NuwanJ/peraSAP-I/PCBs/1. Clock/pdf/pcb_etch_copper_bottom.pdf

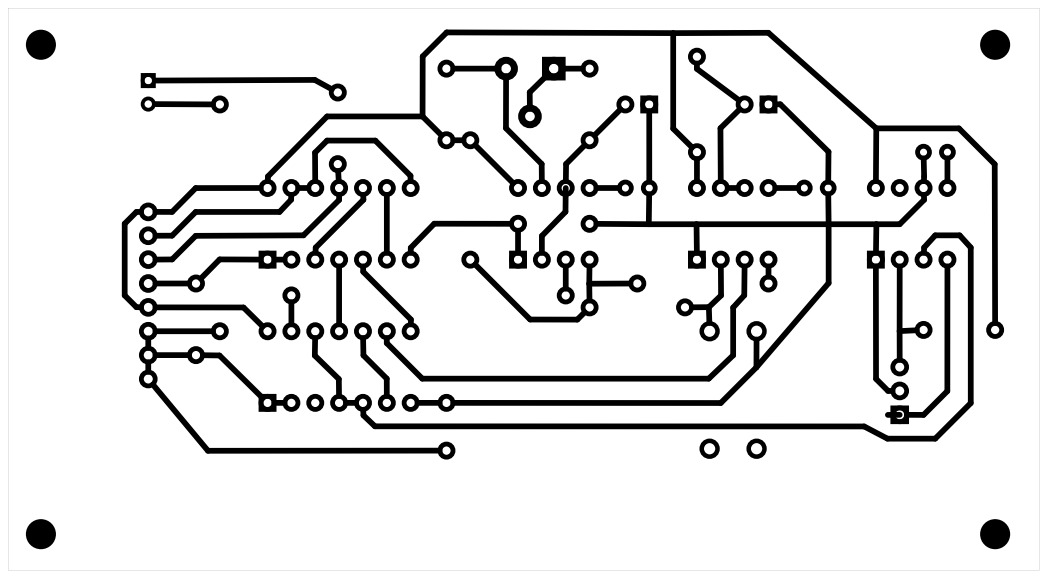
[picture p26: page 1]
