NuwanJ/peraSAP-I/PCBs/1. Clock/pdf/pcb_etch_copper_bottom_mirror.pdf

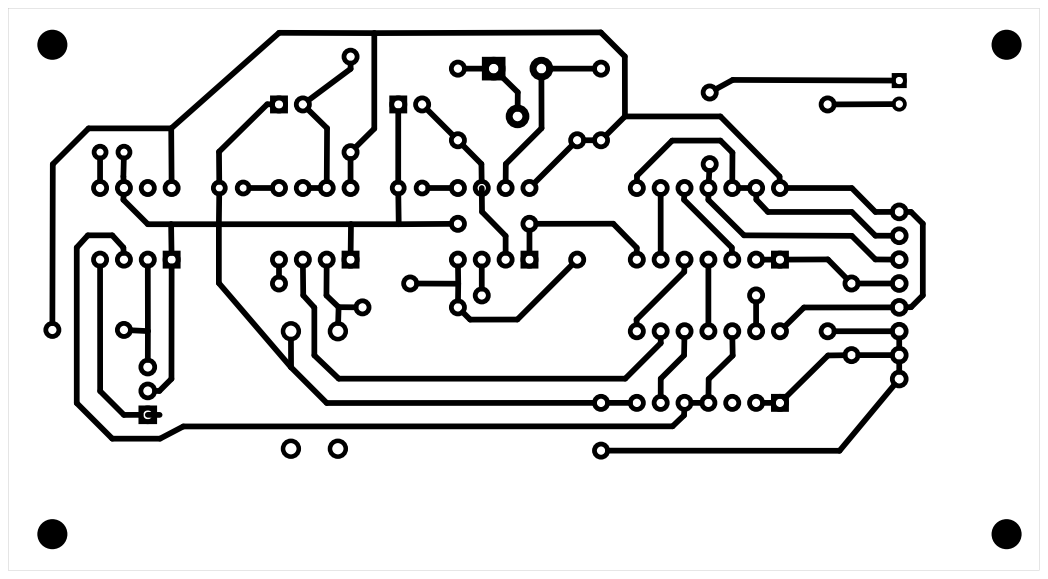
[picture p27: page 1]
