NuwanJ/peraSAP-I/PCBs/1. Clock/pdf/pcb_etch_copper_top.pdf

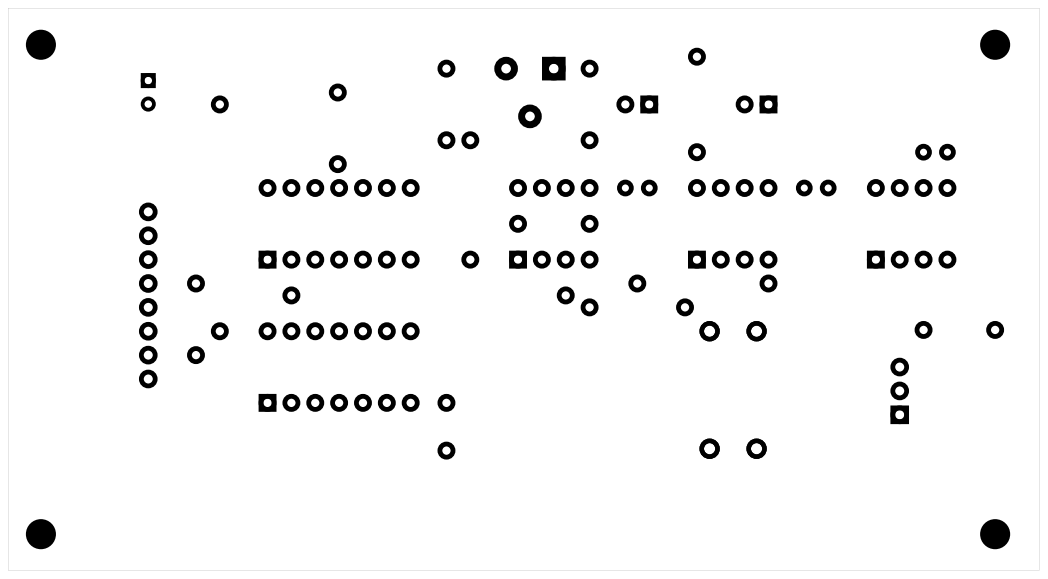
[picture p28: page 1]
