NuwanJ/peraSAP-I/PCBs/1. Clock/pdf/pcb_etch_copper_top_mirror.pdf

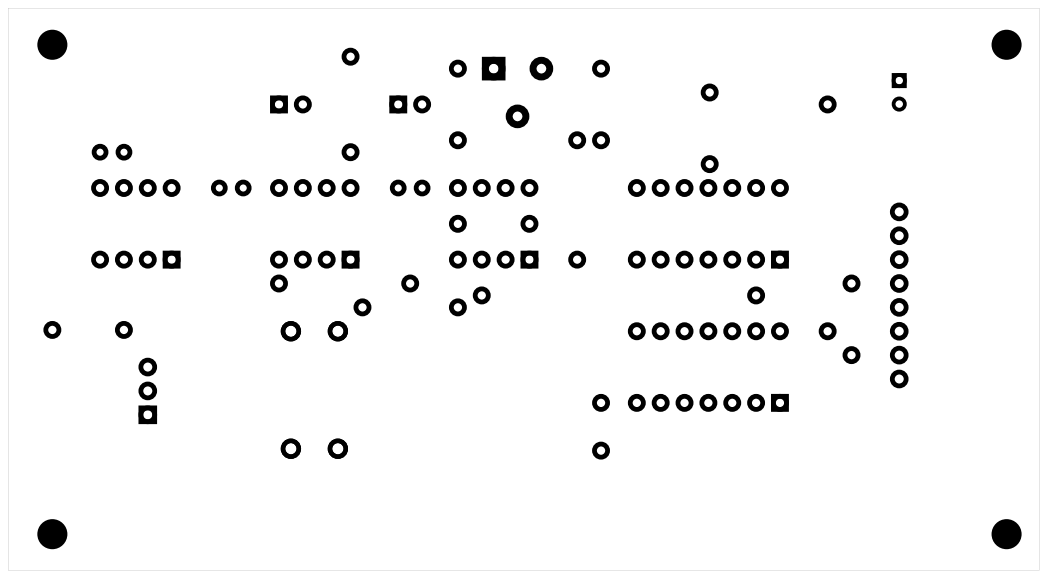
[picture p29: page 1]
