NuwanJ/peraSAP-I/PCBs/1. Clock/pdf/pcb_etch_mask_bottom.pdf

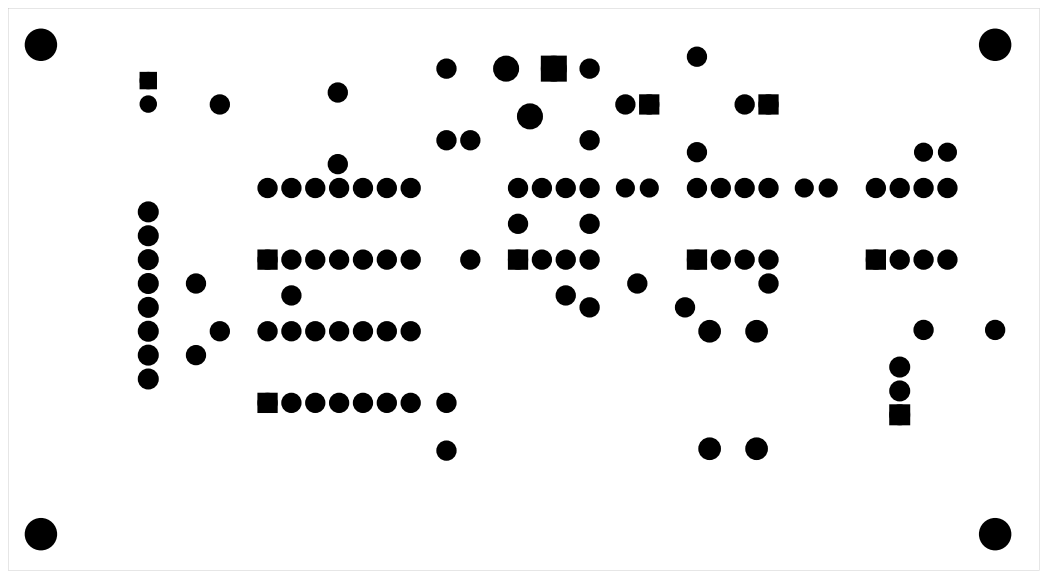
[picture p30: page 1]
