NuwanJ/peraSAP-I/PCBs/1. Clock/pdf/pcb_etch_mask_bottom_mirror.pdf

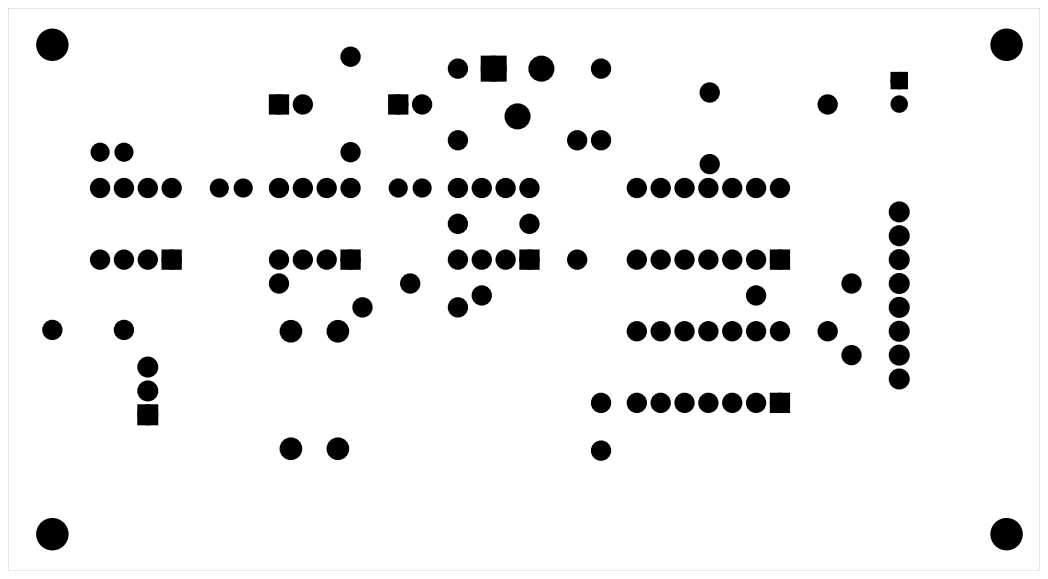
[picture p31: page 1]
