NuwanJ/peraSAP-I/PCBs/1. Clock/pdf/pcb_etch_mask_top.pdf

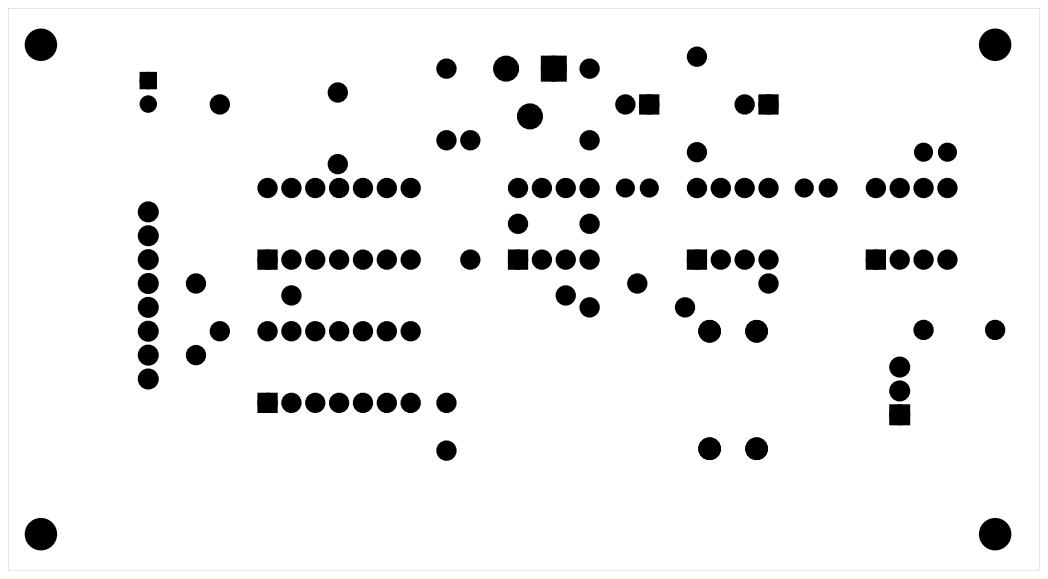
[picture p32: page 1]
