NuwanJ/peraSAP-I/PCBs/1. Clock/pdf/pcb_etch_mask_top_mirror.pdf

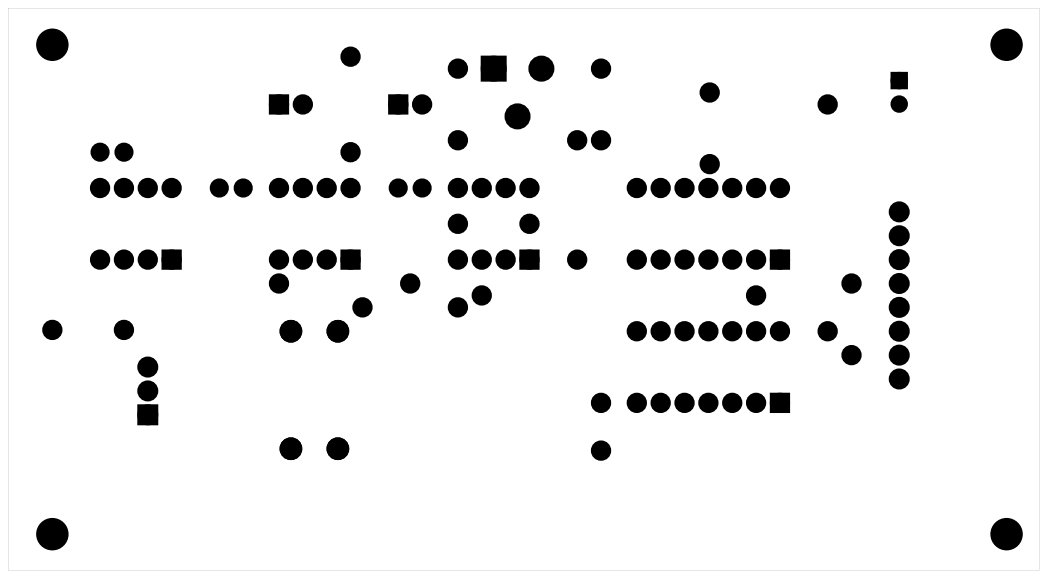
[picture p33: page 1]
