NuwanJ/peraSAP-I/PCBs/1. Clock/pdf/pcb_etch_silk_bottom.pdf

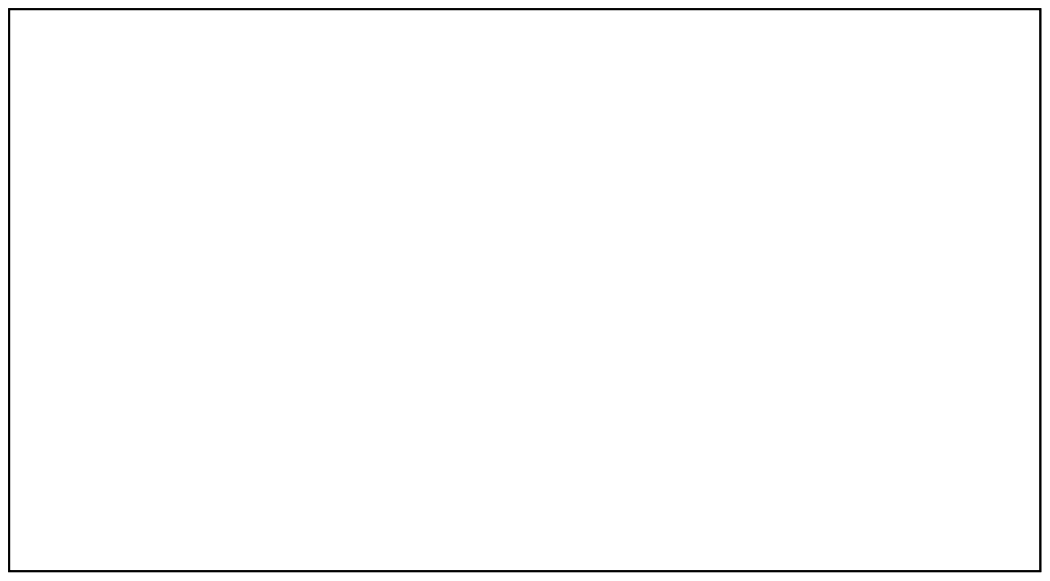
[picture p34: page 1]
