NuwanJ/peraSAP-I/PCBs/1. Clock/pdf/pcb_etch_silk_bottom_mirror.pdf

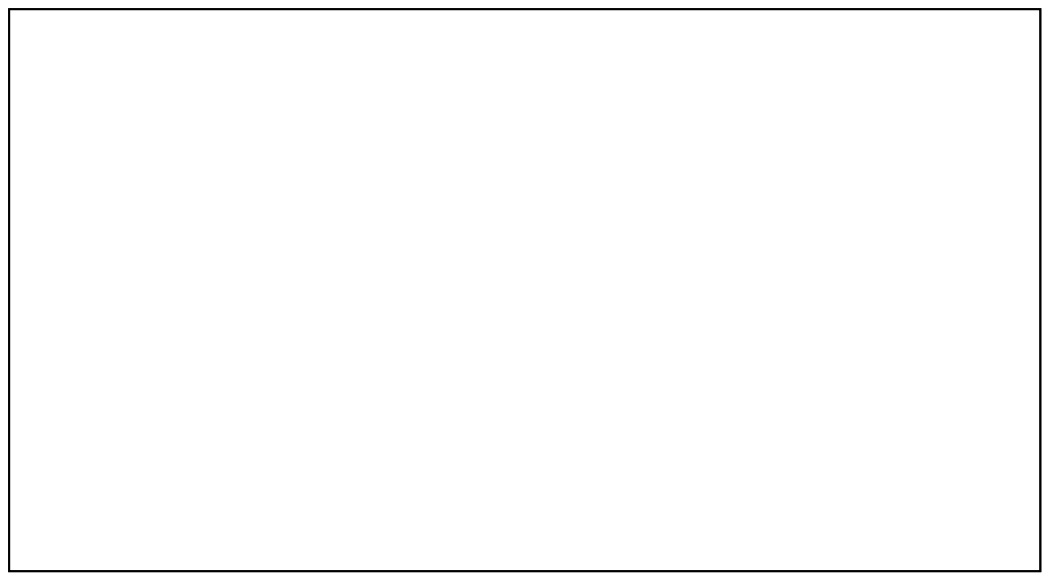
[picture p35: page 1]
