NuwanJ/peraSAP-I/PCBs/1. Clock/pdf/pcb_etch_silk_top.pdf

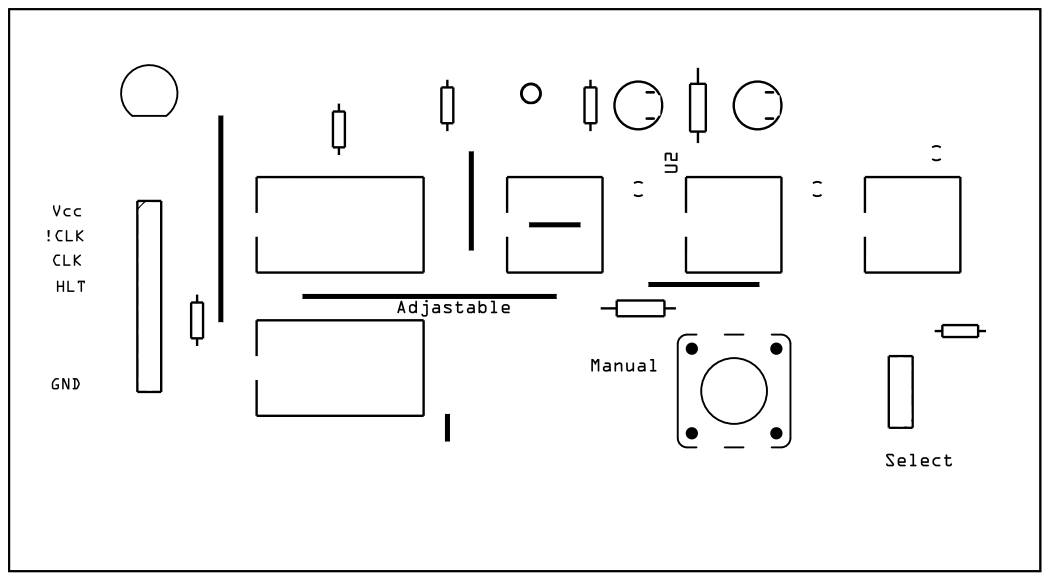
[picture p36: page 1]
