NuwanJ/peraSAP-I/PCBs/1. Clock/pdf/pcb_etch_silk_top_mirror.pdf

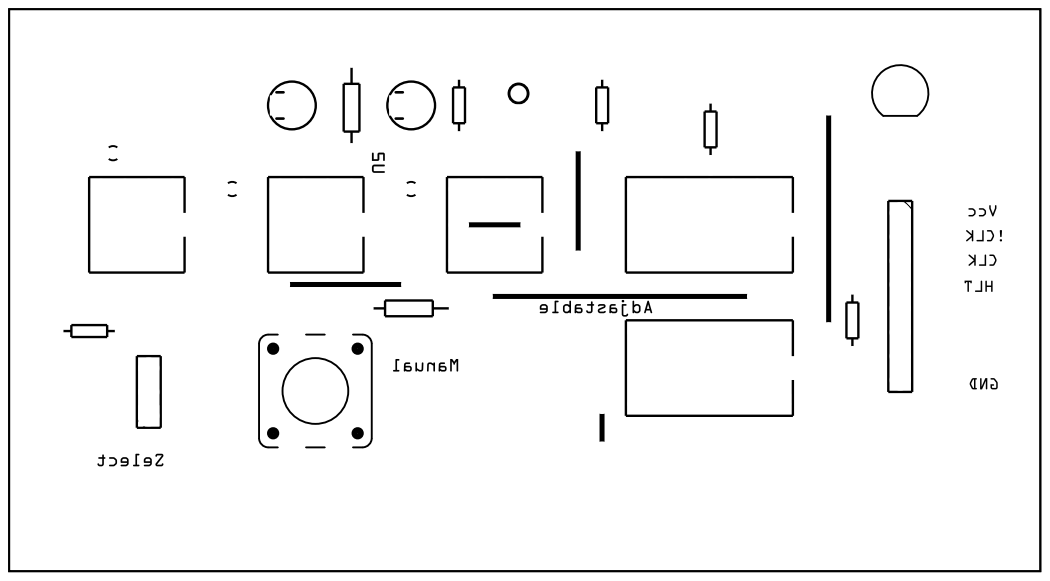
[picture p37: page 1]
