NuwanJ/peraSAP-I/PCBs/2. Registers/pdf/pcb_etch_copper_bottom.pdf

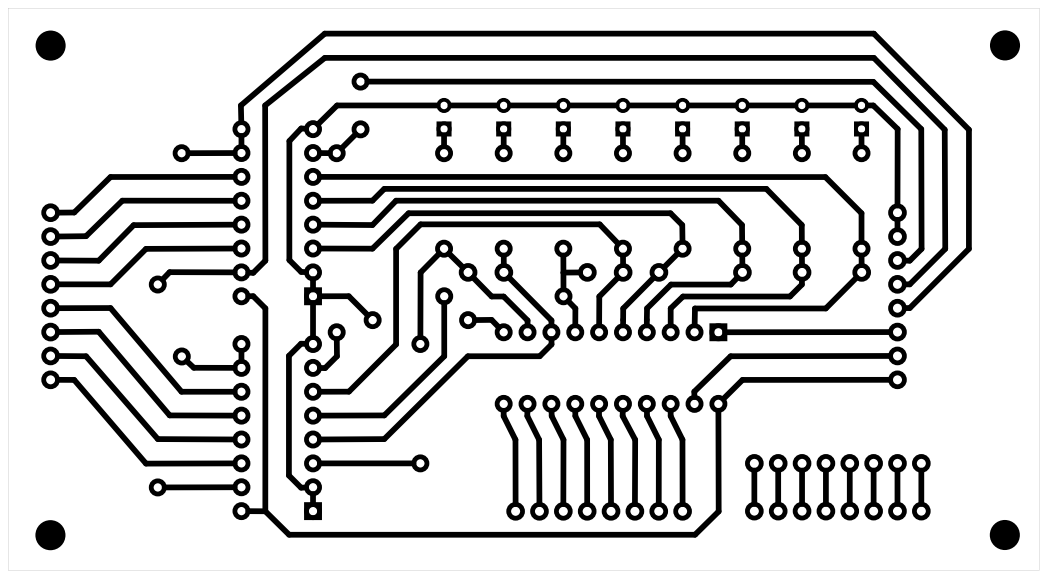
[picture p38: page 1]
