NuwanJ/peraSAP-I/PCBs/2. Registers/pdf/pcb_etch_copper_bottom_mirror.pdf

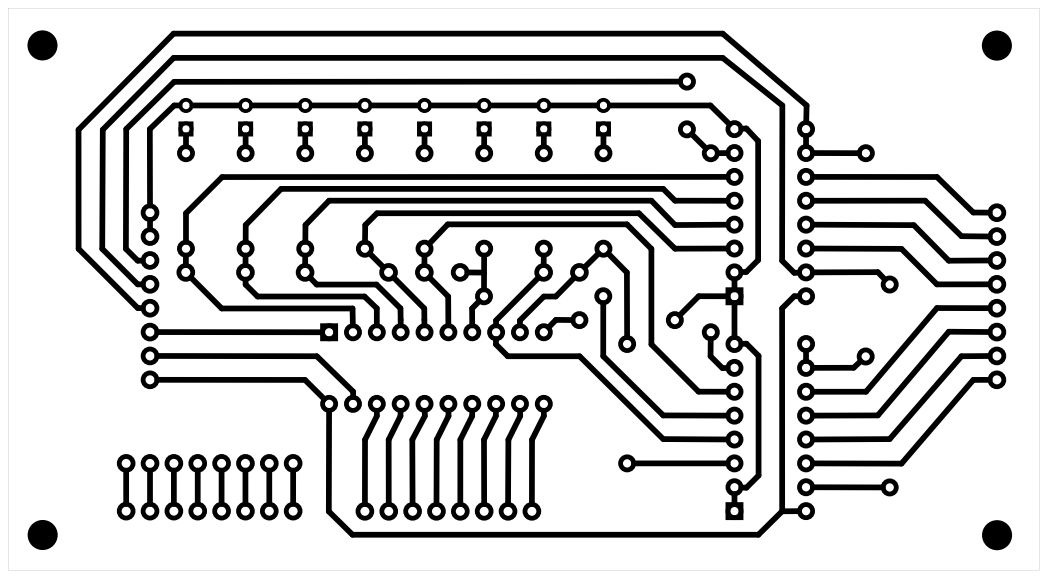
[picture p39: page 1]
