NuwanJ/peraSAP-I/PCBs/2. Registers/pdf/pcb_etch_mask_bottom.pdf

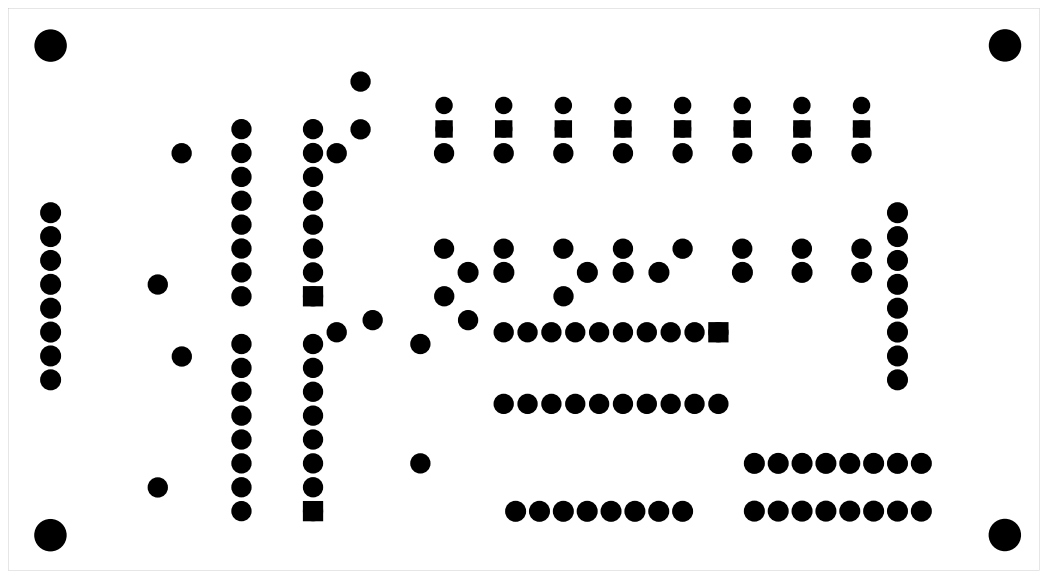
[picture p40: page 1]
