NuwanJ/peraSAP-I/PCBs/2. Registers/pdf/pcb_etch_mask_bottom_mirror.pdf

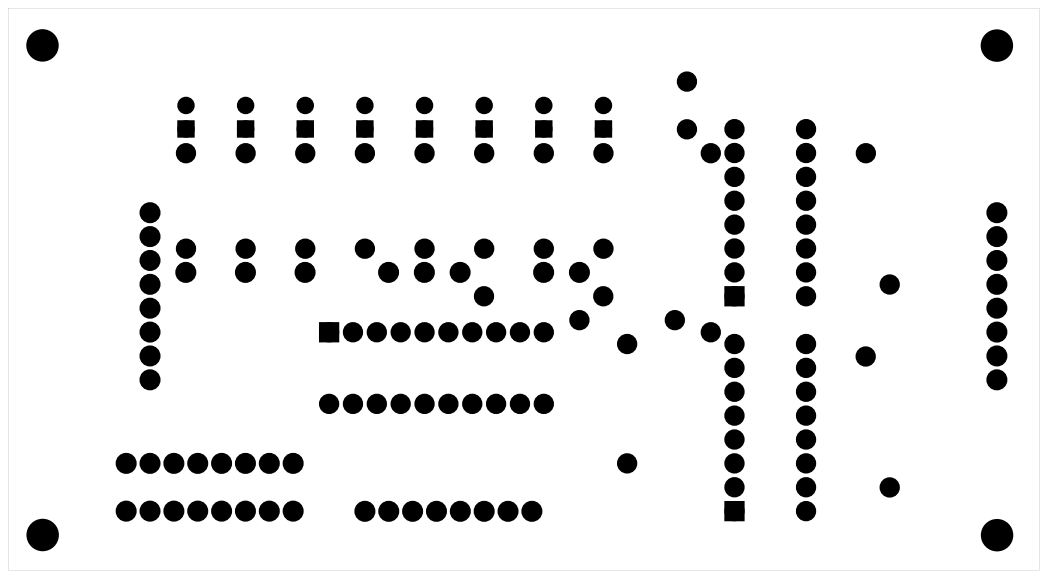
[picture p41: page 1]
