NuwanJ/peraSAP-I/PCBs/3. Program Counter/pdf/pcb3_etch_copper_bottom.pdf

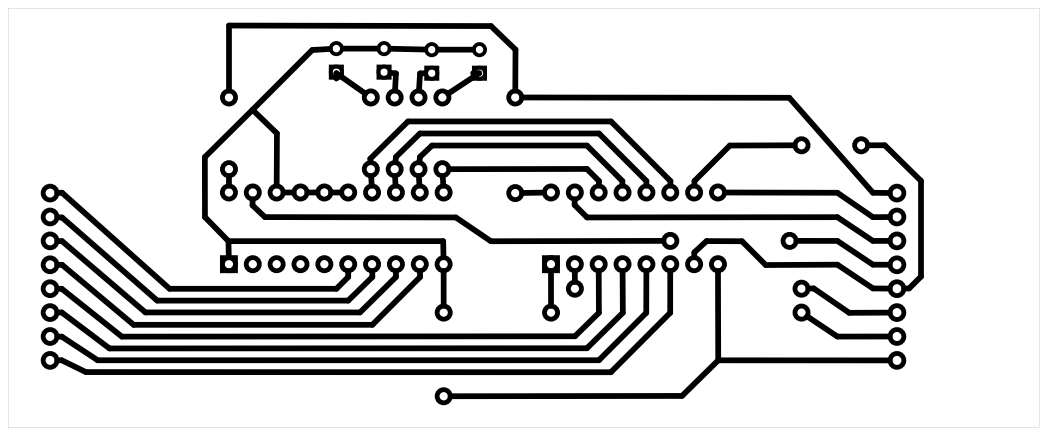
[picture p42: page 1]
