NuwanJ/peraSAP-I/PCBs/3. Program Counter/pdf/pcb3_etch_copper_bottom_mirror.pdf

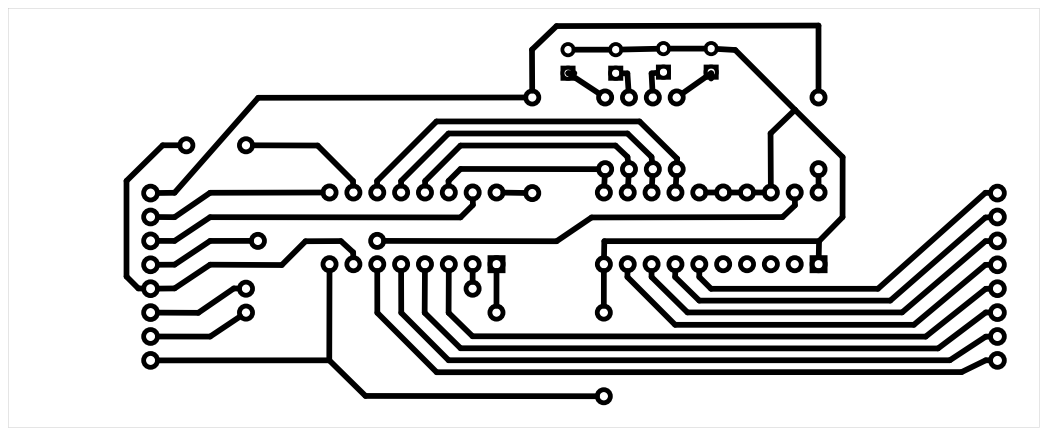
[picture p43: page 1]
