NuwanJ/peraSAP-I/PCBs/3. Program Counter/pdf/pcb3_etch_mask_bottom.pdf

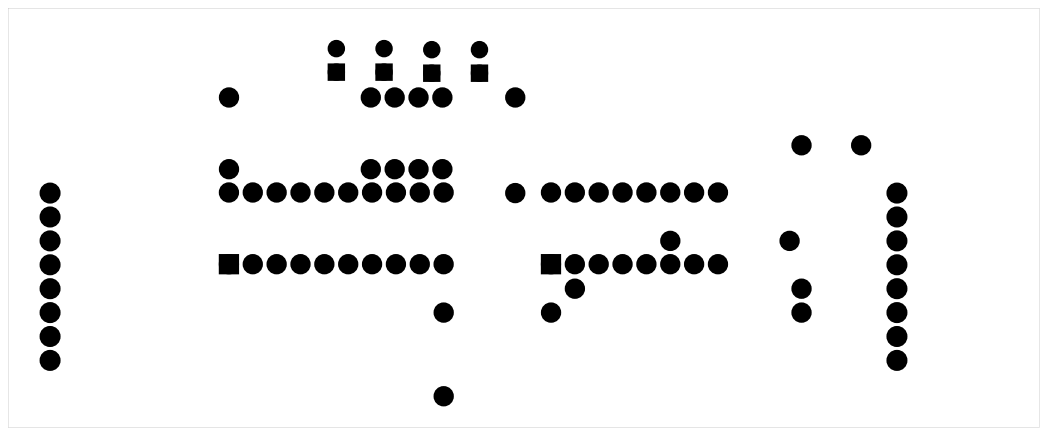
[picture p44: page 1]
