NuwanJ/peraSAP-I/PCBs/3. Program Counter/pdf/pcb3_etch_mask_bottom_mirror.pdf

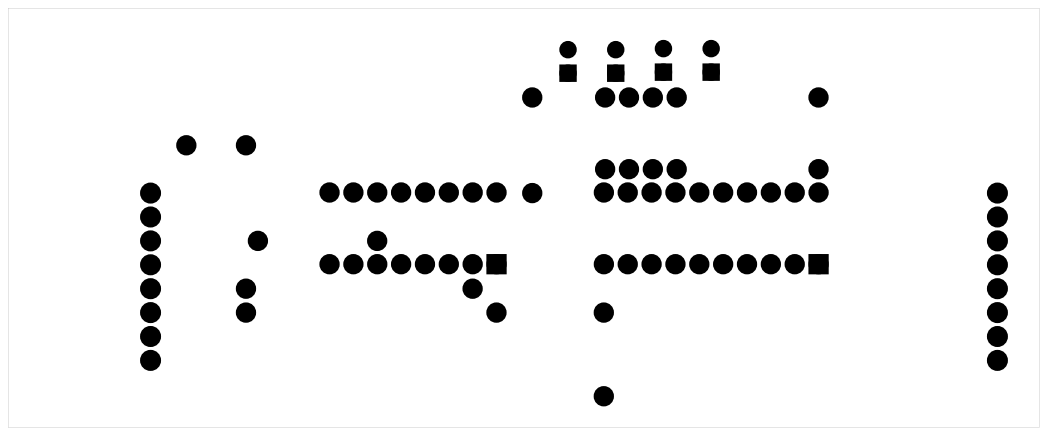
[picture p45: page 1]
