NuwanJ/peraSAP-I/PCBs/3. Program Counter/pdf/pcb3_etch_silk_bottom.pdf

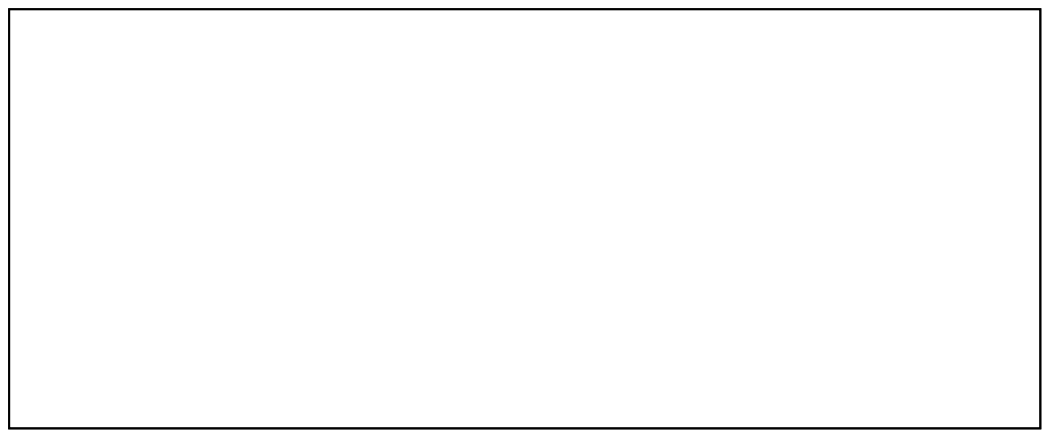
[picture p46: page 1]
