NuwanJ/peraSAP-I/PCBs/3. Program Counter/pdf/pcb3_etch_silk_bottom_mirror.pdf

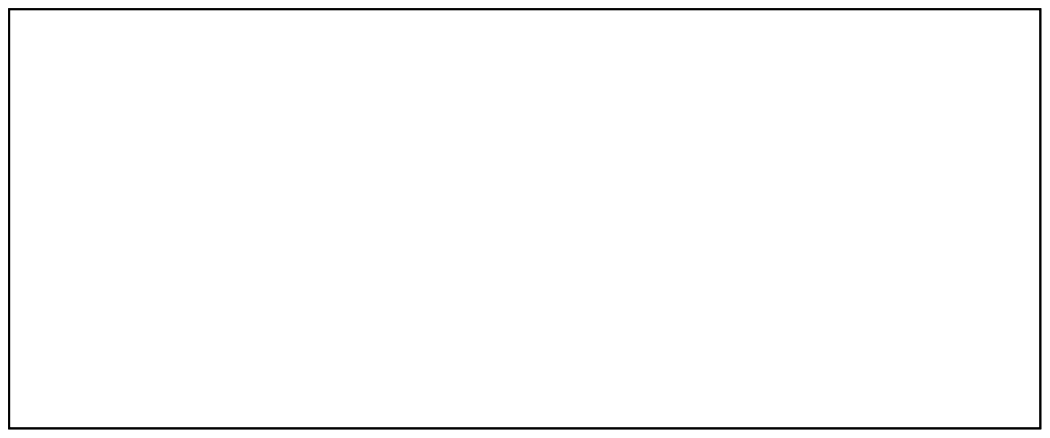
[picture p47: page 1]
