NuwanJ/peraSAP-I/PCBs/3. Program Counter/pdf/pcb_etch_copper_bottom.pdf

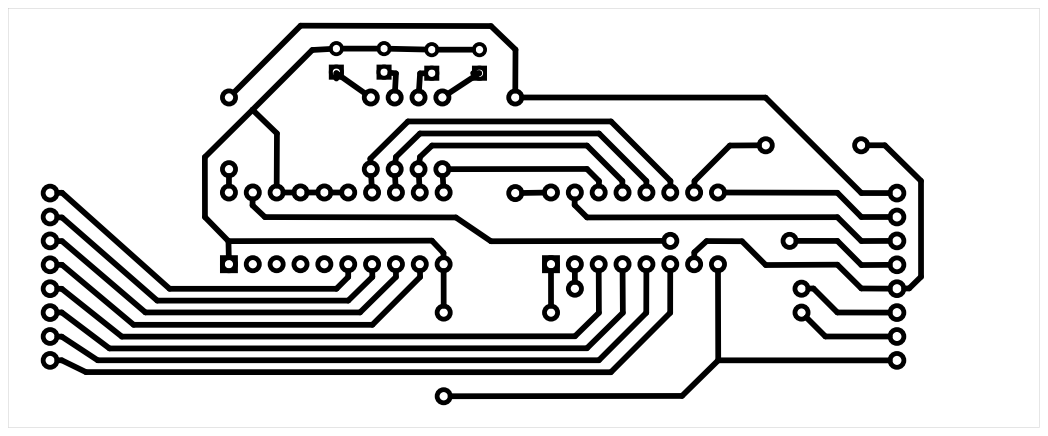
[picture p48: page 1]
