NuwanJ/peraSAP-I/PCBs/3. Program Counter/pdf/pcb_etch_copper_bottom_mirror.pdf

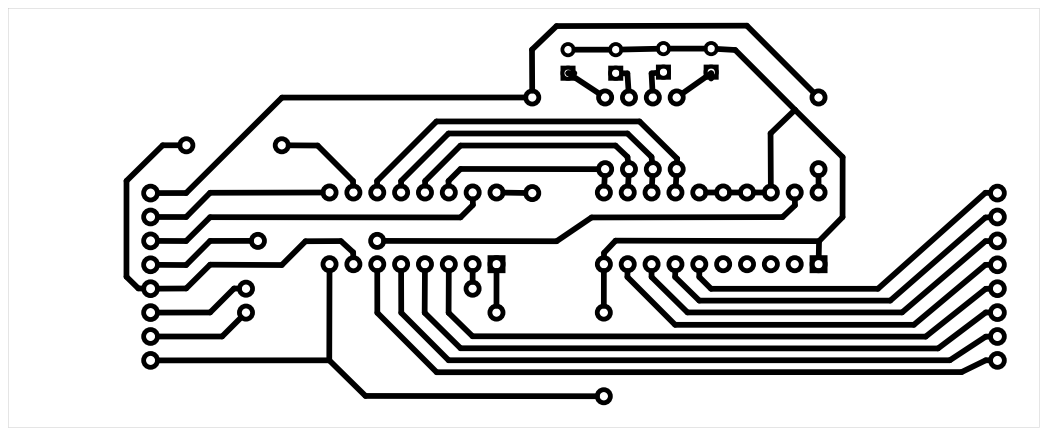
[picture p49: page 1]
