NuwanJ/peraSAP-I/PCBs/3. Program Counter/pdf/pcb_etch_mask_bottom.pdf

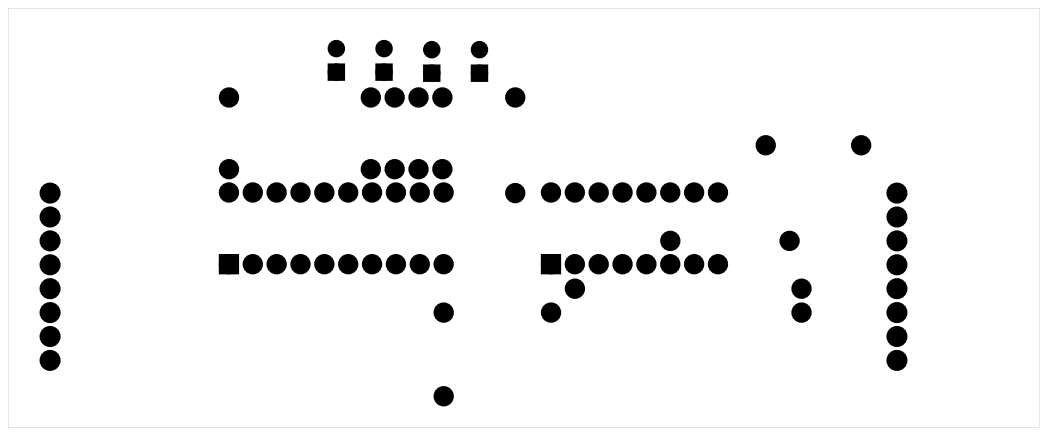
[picture p50: page 1]
