NuwanJ/peraSAP-I/PCBs/3. Program Counter/pdf/pcb_etch_mask_bottom_mirror.pdf

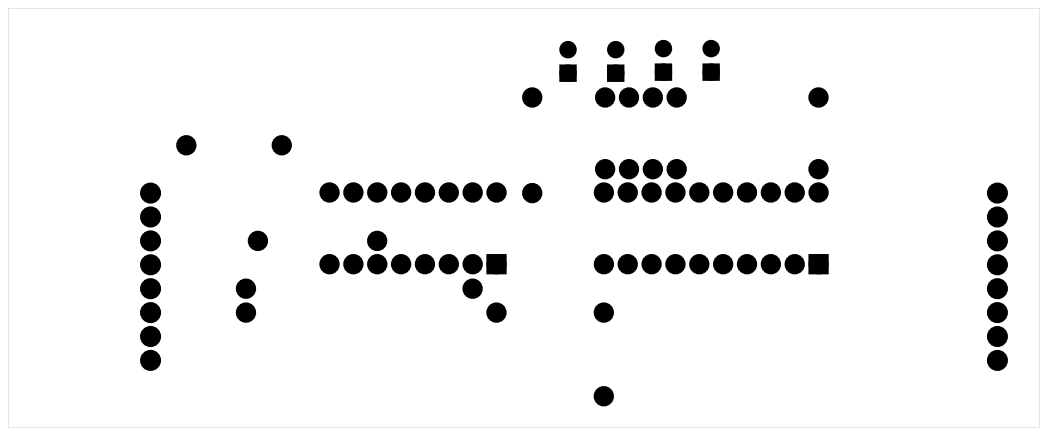
[picture p51: page 1]
