NuwanJ/peraSAP-I/PCBs/4. ALU/pdf/pcb_etch_copper_bottom.pdf

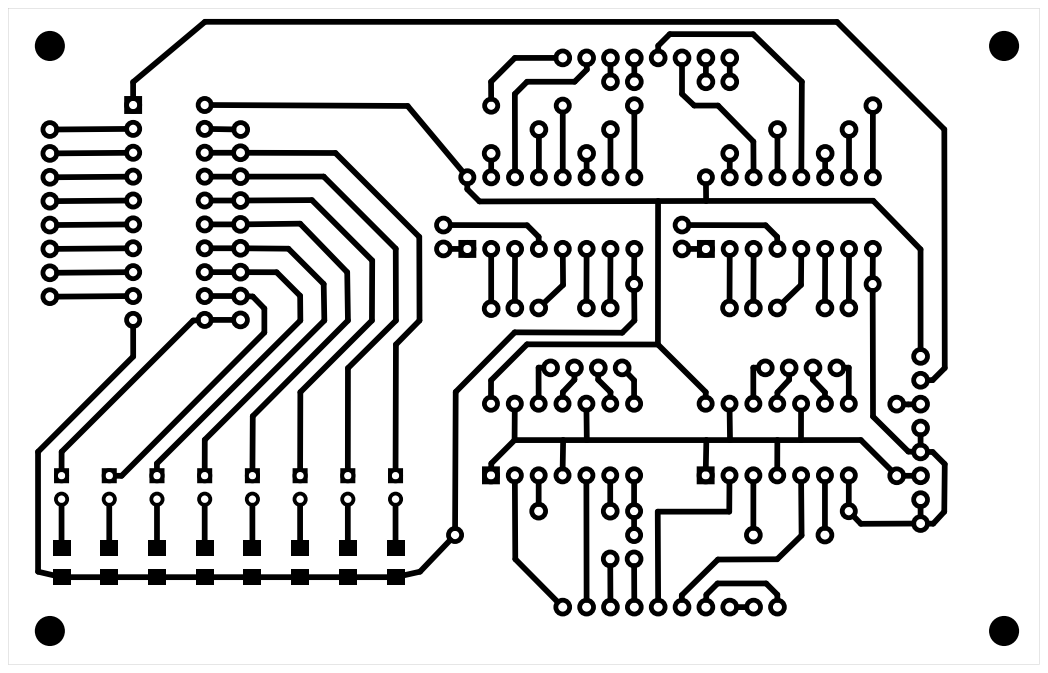
[picture p52: page 1]
