NuwanJ/peraSAP-I/PCBs/4. ALU/pdf/pcb_etch_copper_bottom_mirror.pdf

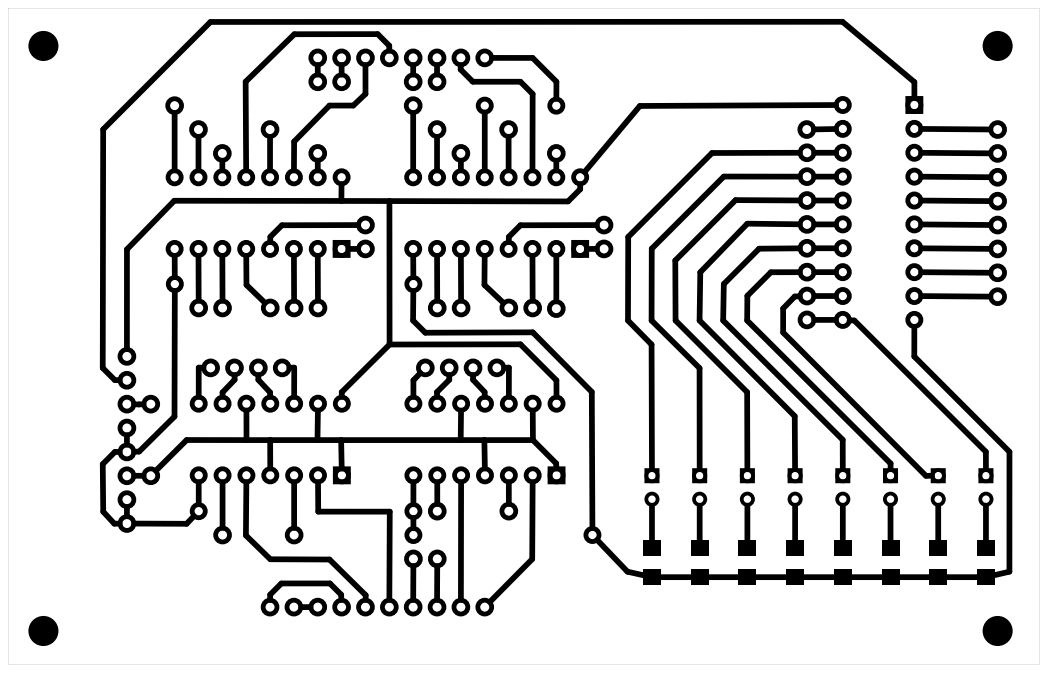
[picture p53: page 1]
