NuwanJ/peraSAP-I/PCBs/4. ALU/pdf/pcb_etch_mask_bottom.pdf

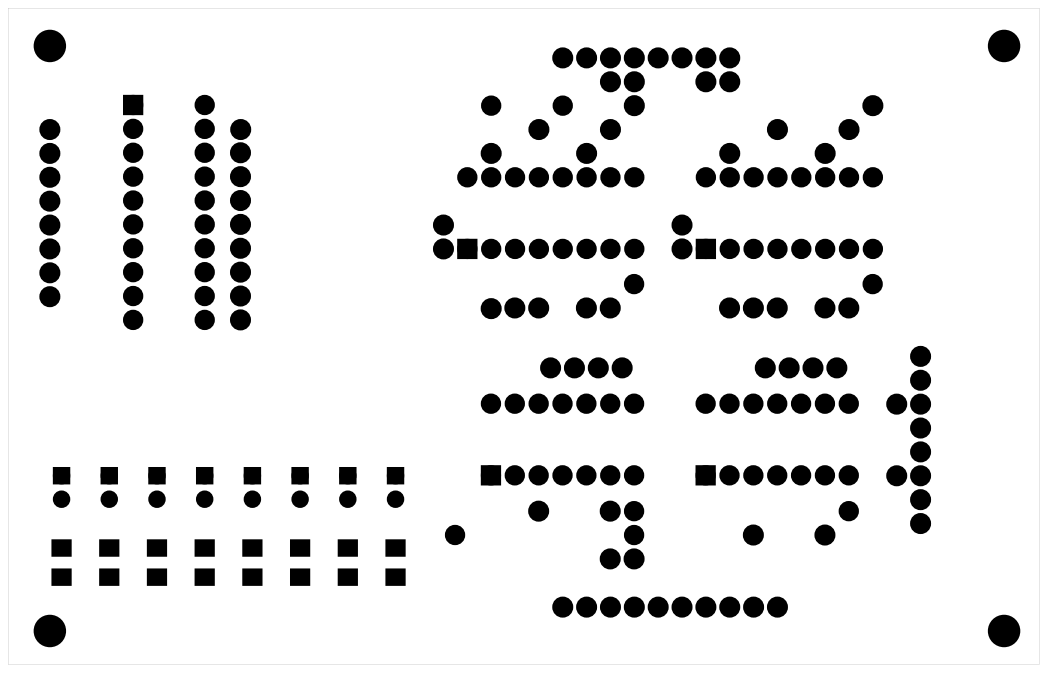
[picture p54: page 1]
