NuwanJ/peraSAP-I/PCBs/4. ALU/pdf/pcb_etch_mask_bottom_mirror.pdf

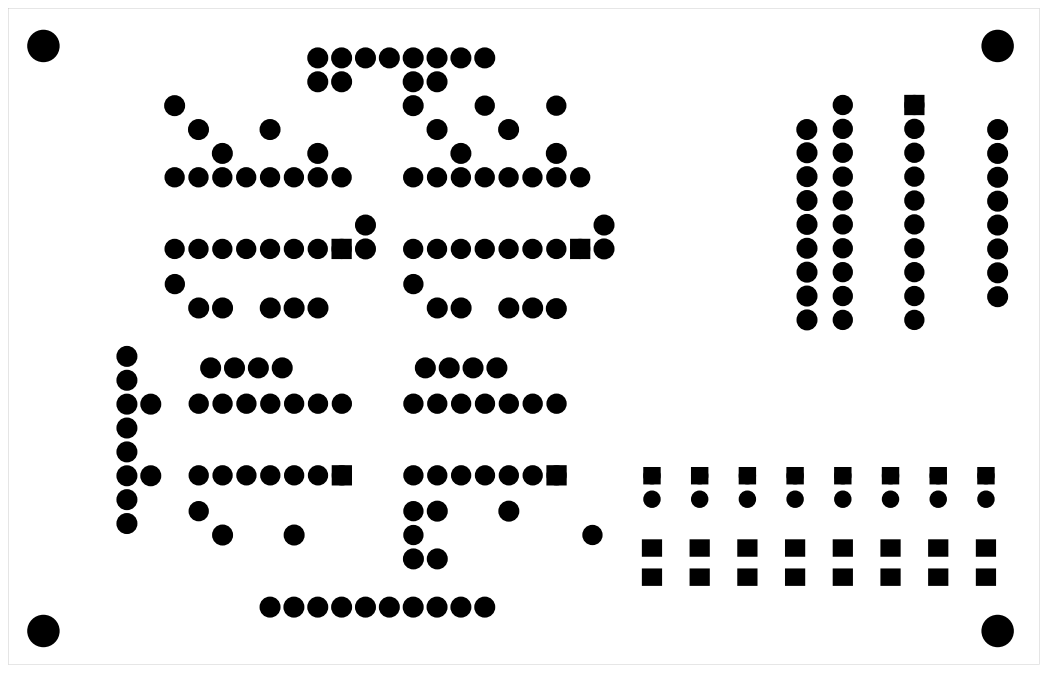
[picture p55: page 1]
