NuwanJ/peraSAP-I/PCBs/4. ALU/pdf/pcb_etch_silk_bottom.pdf

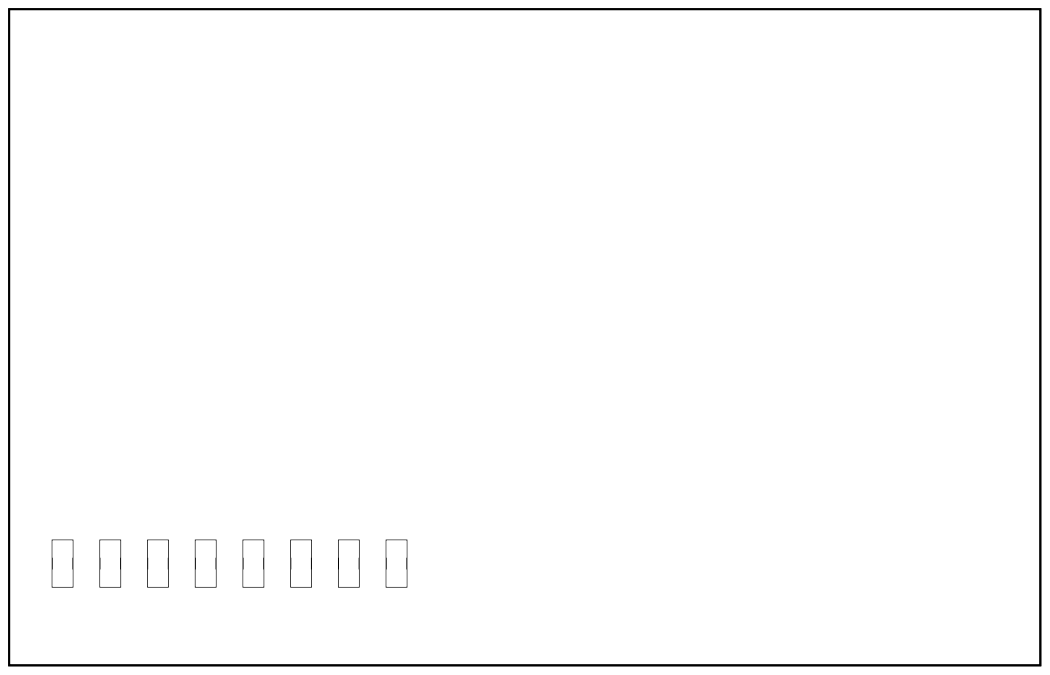
[picture p56: page 1]
