NuwanJ/peraSAP-I/PCBs/4. ALU/pdf/pcb_etch_silk_bottom_mirror.pdf

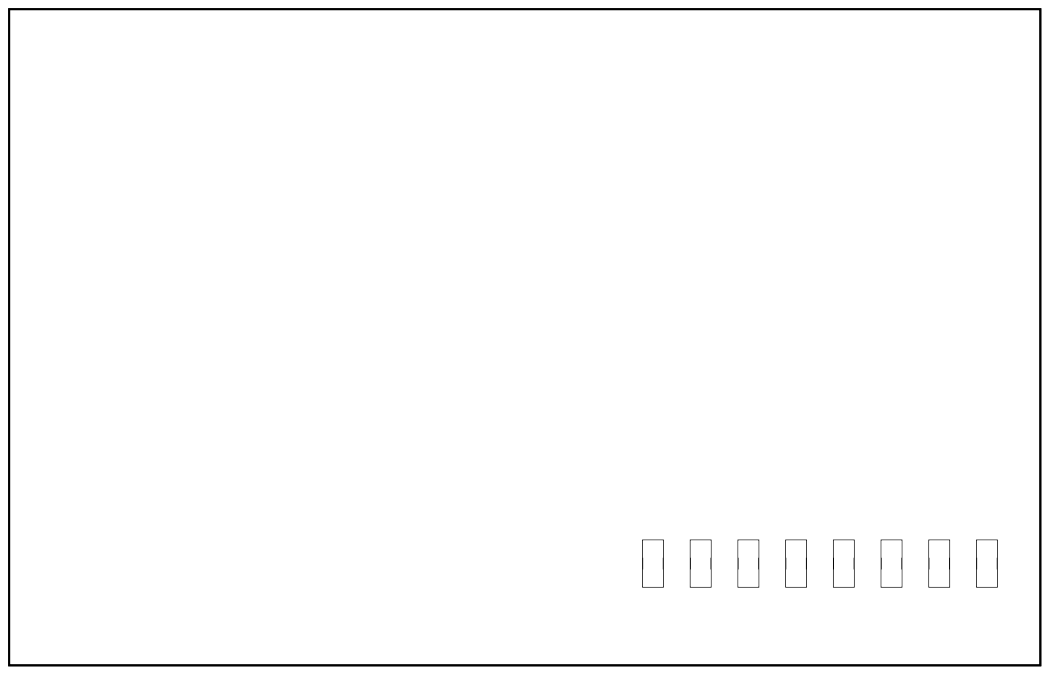
[picture p57: page 1]
