NuwanJ/peraSAP-I/PCBs/5. Output Register/pdf/pcb_etch_copper_bottom.pdf

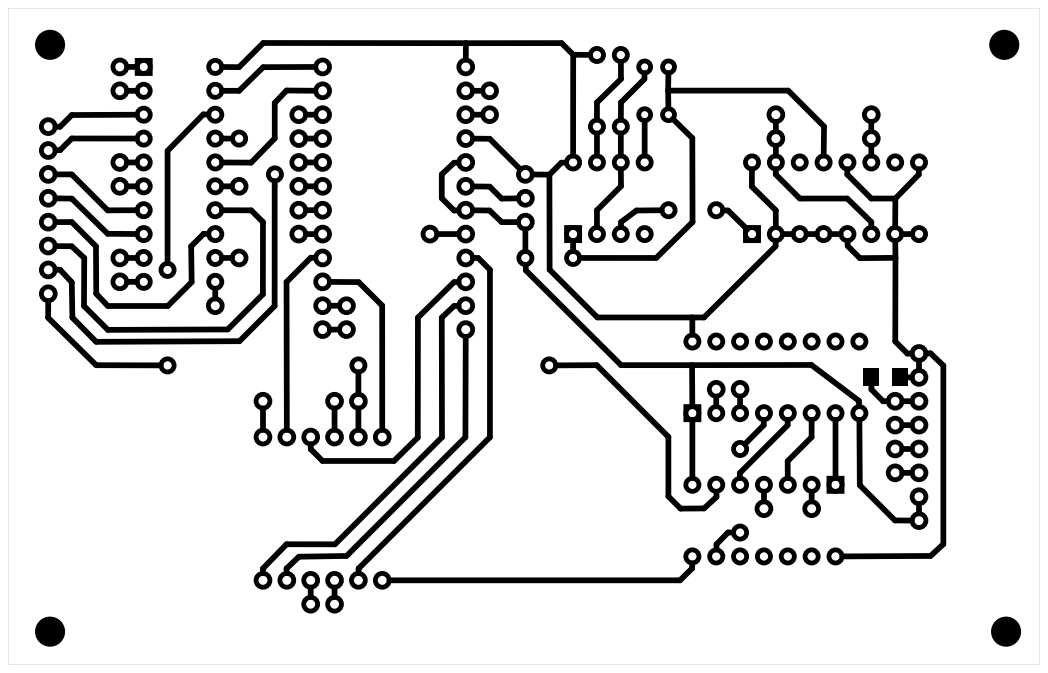
[picture p58: page 1]
