NuwanJ/peraSAP-I/PCBs/5. Output Register/pdf/pcb_etch_copper_bottom_mirror.pdf

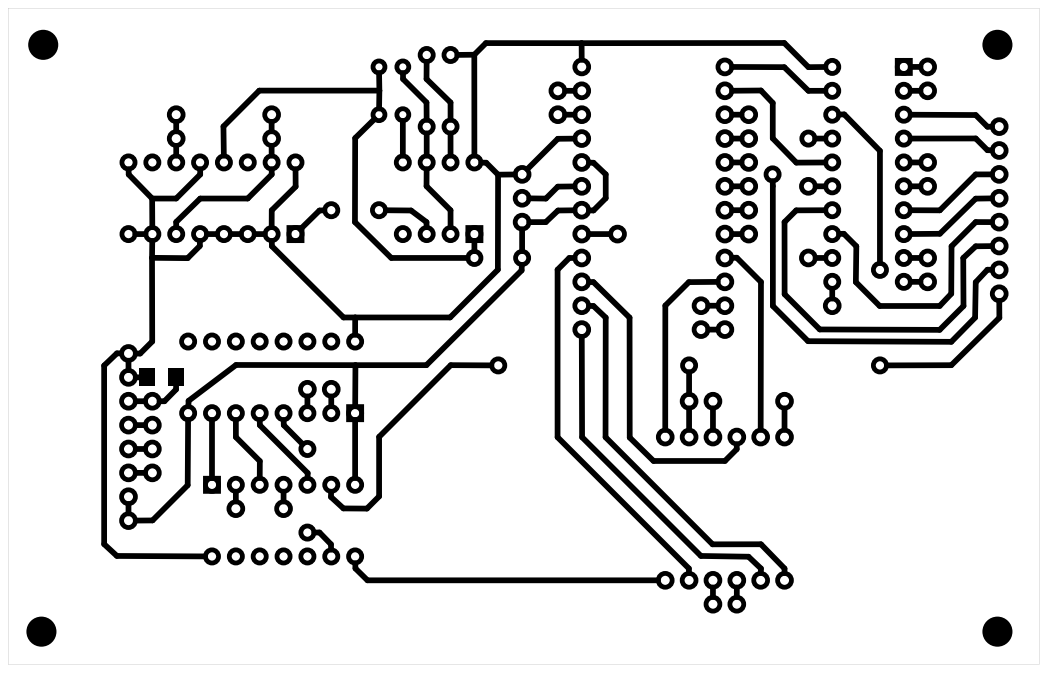
[picture p59: page 1]
