NuwanJ/peraSAP-I/PCBs/5. Output Register/pdf/pcb_etch_mask_bottom.pdf

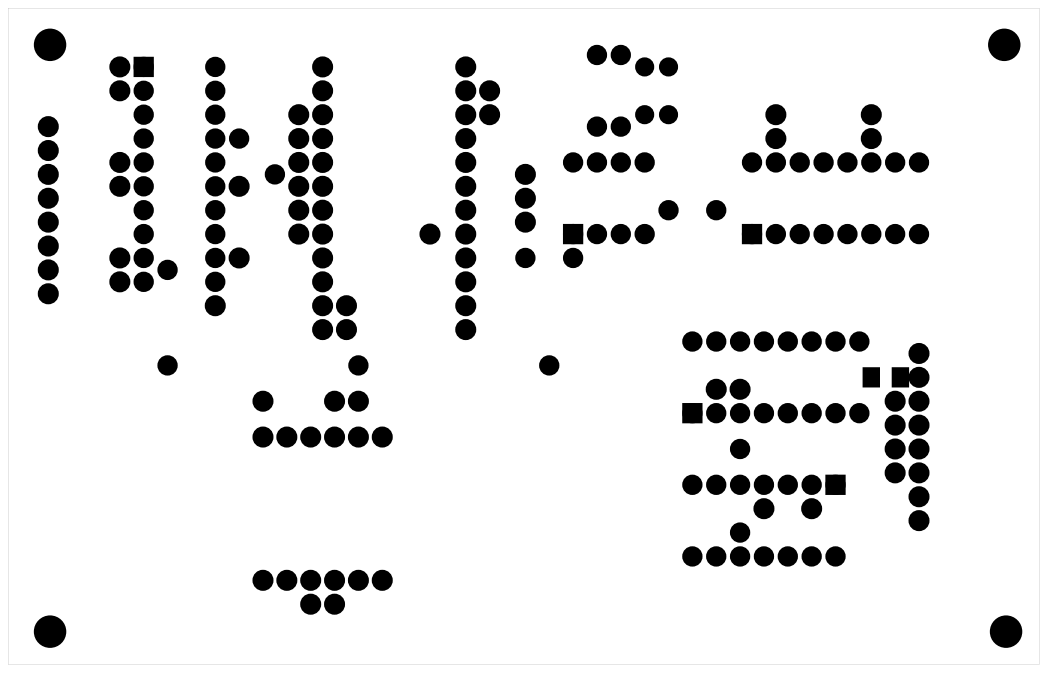
[picture p60: page 1]
