NuwanJ/peraSAP-I/PCBs/5. Output Register/pdf/pcb_etch_mask_bottom_mirror.pdf

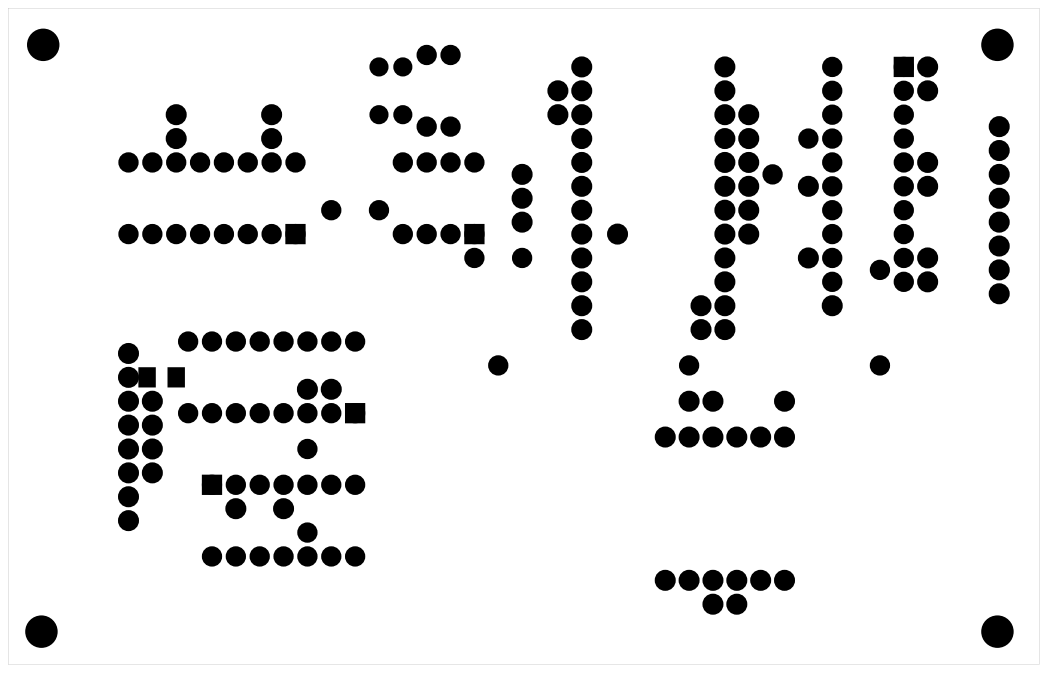
[picture p61: page 1]
