NuwanJ/peraSAP-I/PCBs/5. Output Register/pdf/pcb_etch_silk_bottom.pdf

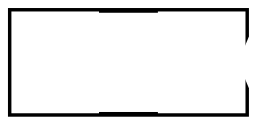
[picture p62: page 1]
