NuwanJ/peraSAP-I/PCBs/5. Output Register/pdf/pcb_etch_silk_bottom_mirror.pdf

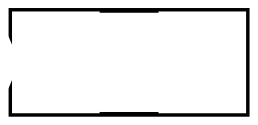
[picture p63: page 1]
