NuwanJ/peraSAP-I/PCBs/8. Motherboard/pdf/pcb_etch_copper_bottom.pdf

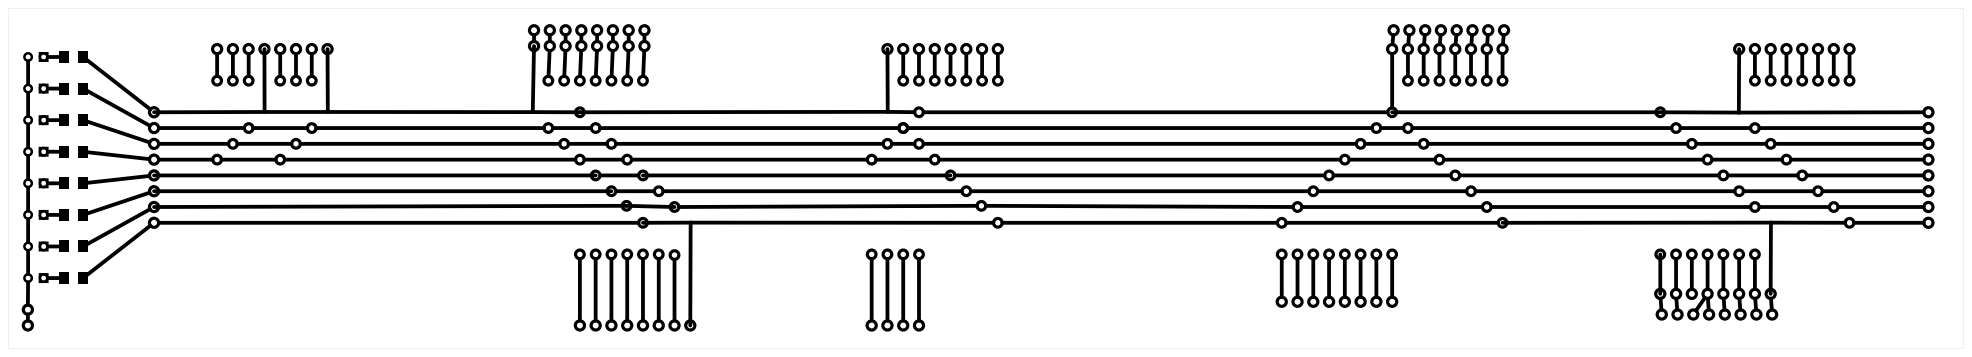
[picture p64: page 1]
