NuwanJ/peraSAP-I/PCBs/8. Motherboard/pdf/pcb_etch_copper_bottom_mirror.pdf

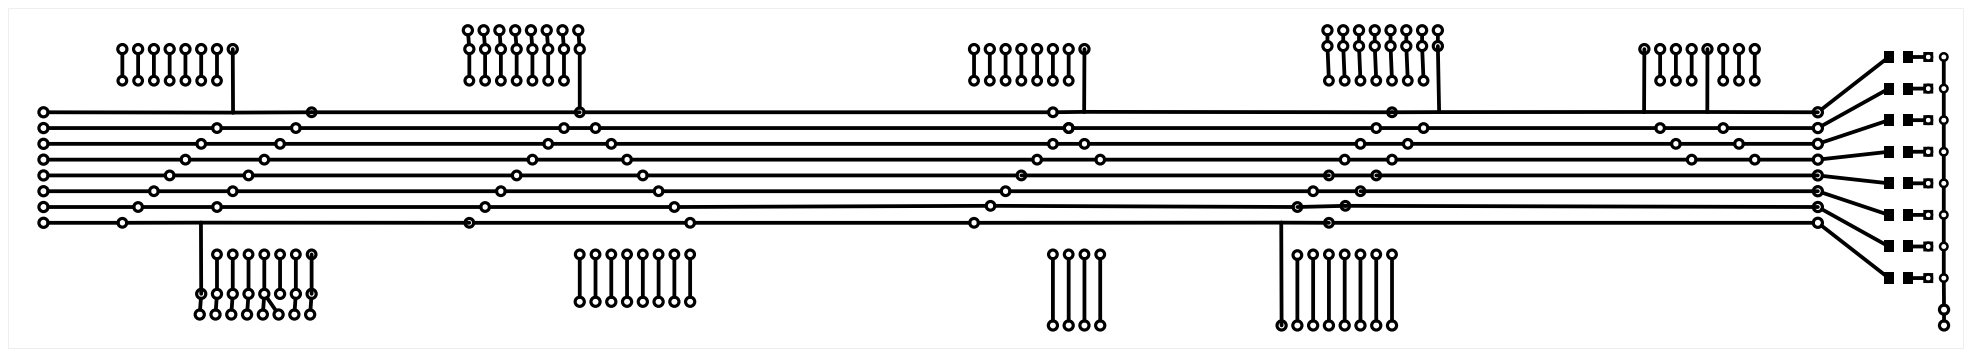
[picture p65: page 1]
